carletz/MultiSensor/Hardware/20250601_090914.jpg

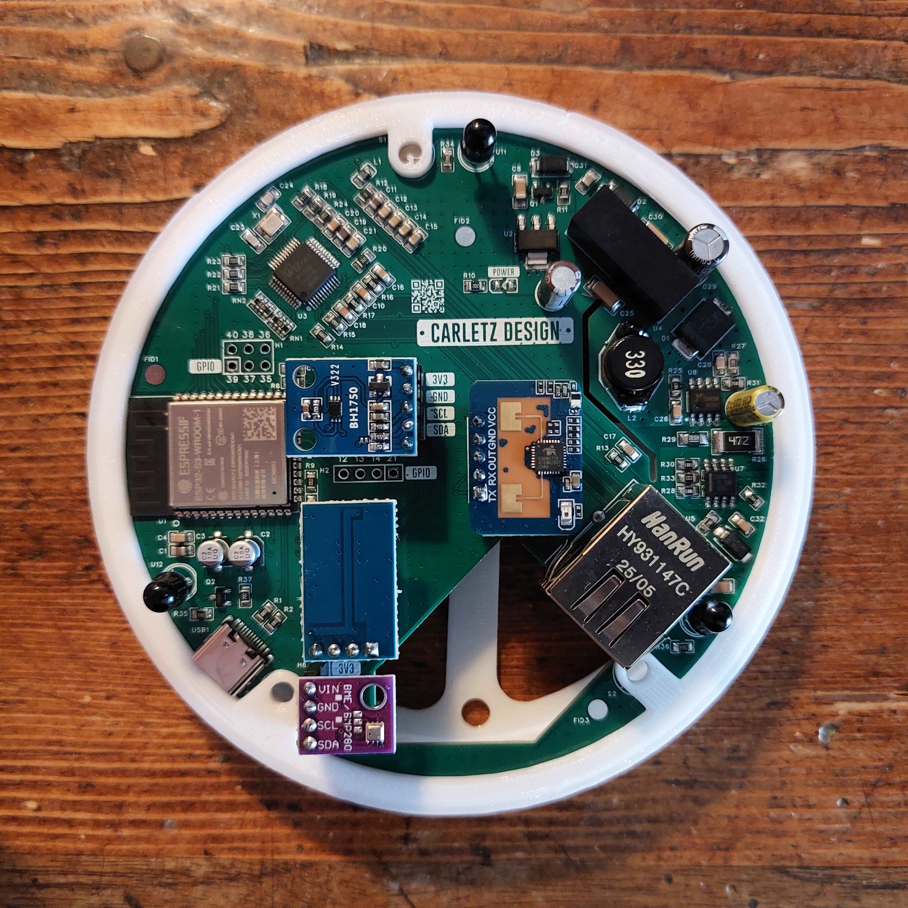
Hardware/20250601_090914.jpg
