carletz/MultiSensor/Hardware/20250601_091432.jpg

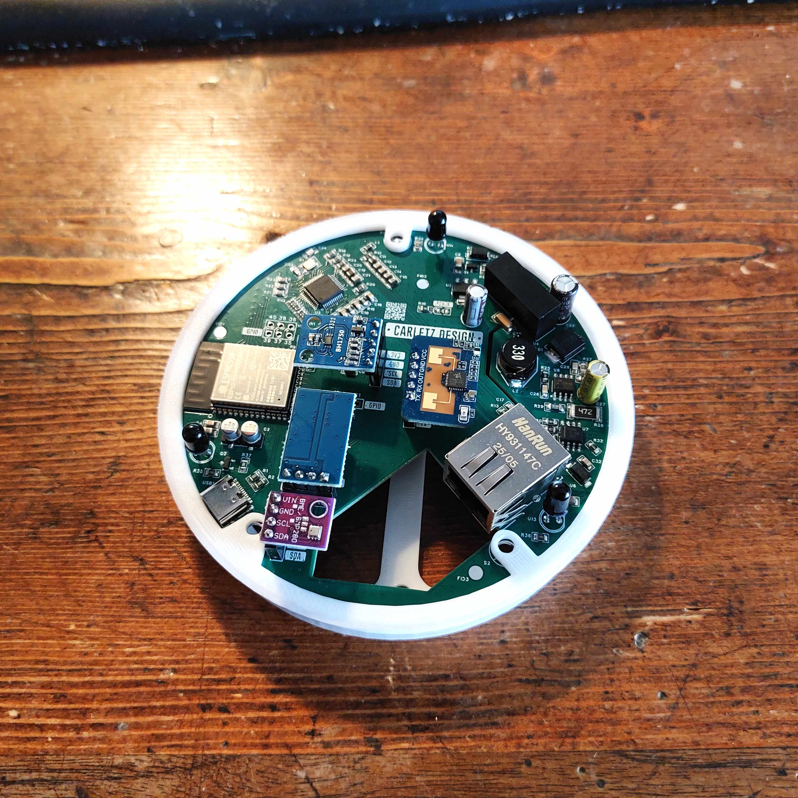
Hardware/20250601_091432.jpg
